zimeke/Arduino-Clone/Photos/Arduino Clone compared to Arduino UNO.jpg

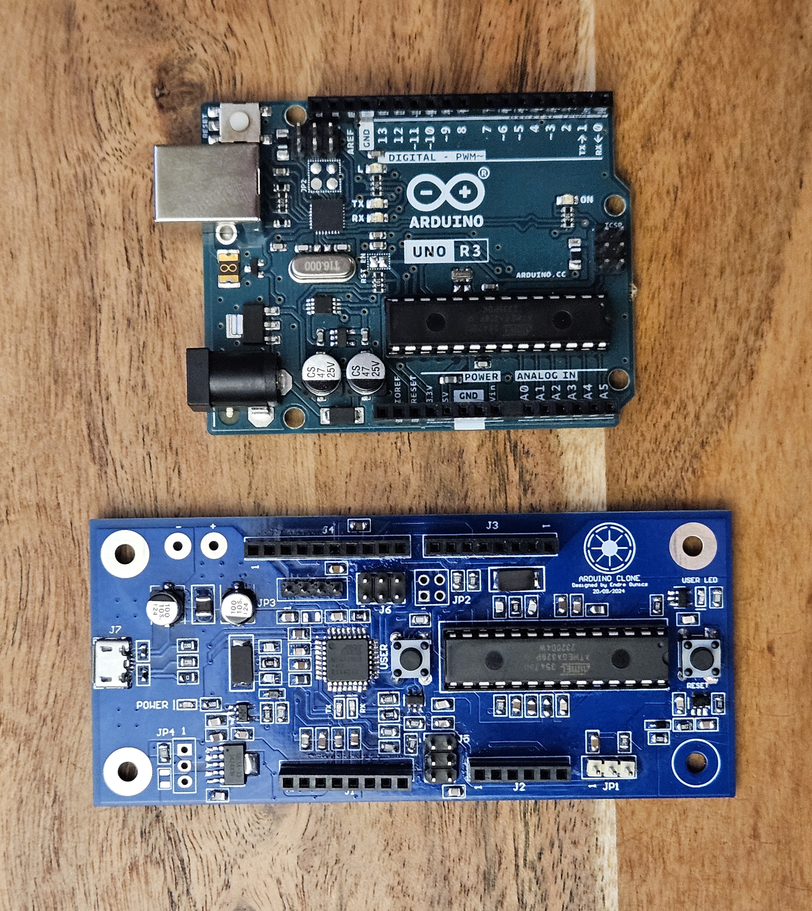
Photos/Arduino Clone compared to Arduino UNO.jpg
