zimeke/Arduino-Clone/3D_models_for_Altium_Designer/M20-7821046_asm.stp

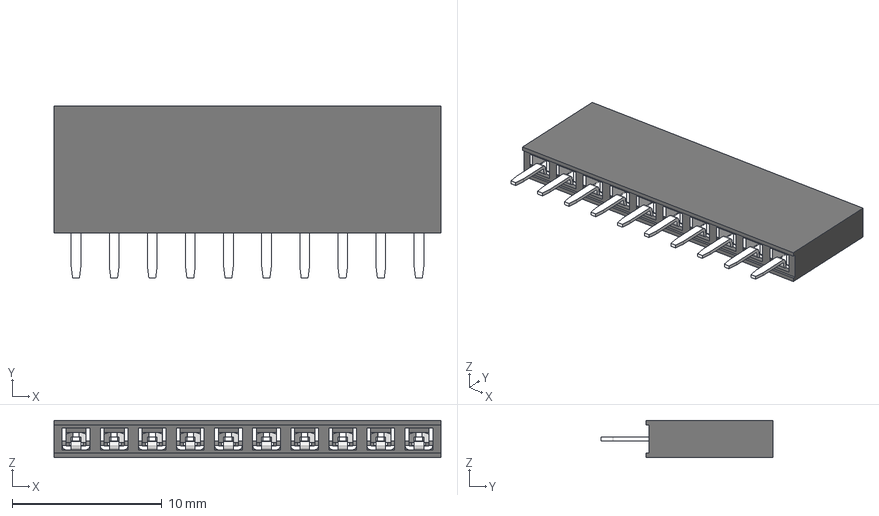
[picture p22: CAD file, 2024-10-12]
3D_models_for_Altium_Designer/M20-7821046_asm.stp
25.8 x 11.5 x 2.50 mm
M20-78210_MOULD
M20-782_CONTACT x 10
