zimeke/Arduino-Clone/3D_models_for_Altium_Designer/67997-106HLF.step

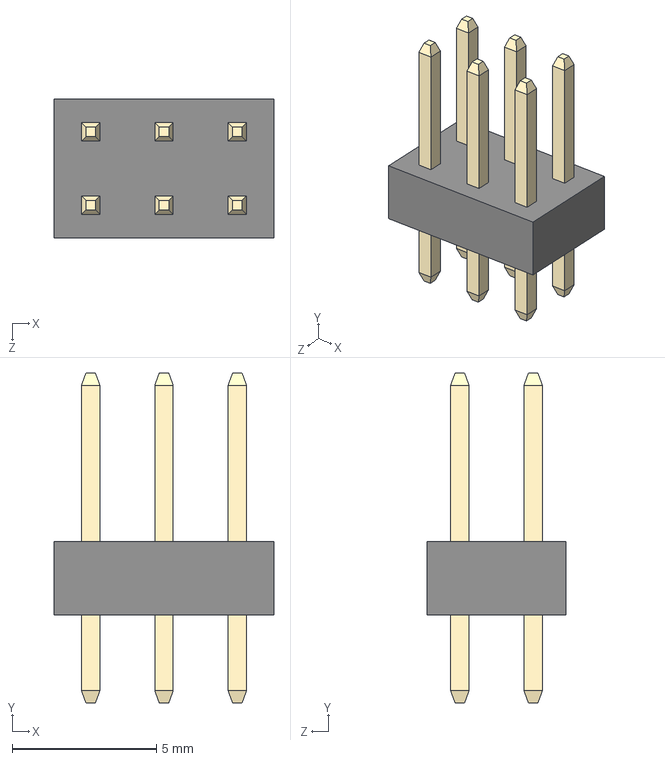
[picture p23: CAD file, 2024-10-12]
3D_models_for_Altium_Designer/67997-106HLF.step
7.62 x 11.4 x 4.83 mm
