zimeke/Arduino-Clone/3D_models_for_Altium_Designer/m20-7820646.stp

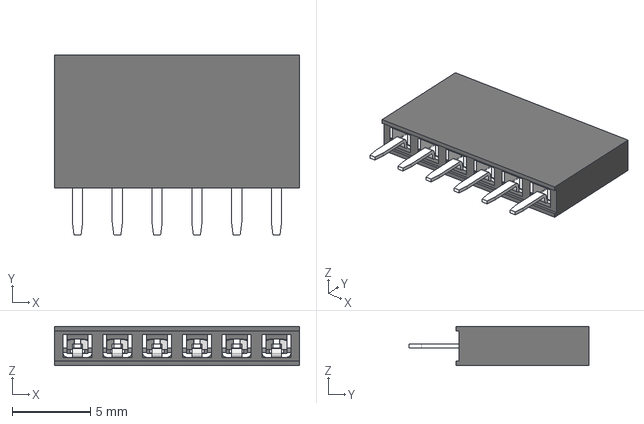
[picture p24: CAD file, 2024-10-12]
3D_models_for_Altium_Designer/m20-7820646.stp
15.6 x 11.5 x 2.50 mm
